ARTS-Laboratory/Sensor-Package-Access-Hub/system_development/V0.3.2/ELCT403/nrf24RX_loraTX_TEENSY/water.h

#define MAX_HEIGHT_VAL 14

const char * height_header[] = {"Date",	"Time", "Dist1",	"Dist2",	"Dist3",	"Dist4",	"Dist5",	"Avg Dist (cm)",
                         "Temp (C)",	"Humidity",	"Pressure",	"Voltage",	"Current (mA)",	"Power (mW)"};
/*
12/1/2025 12:40		-->		1764610800
12/1/2025 12:45		-->		1764611100
12/1/2025 13:00		-->		1764612000
12/1/2025 13:15		-->		1764612900
12/1/2025 13:30		-->		1764613800
*/

double height_data[5][MAX_HEIGHT_VAL] = {
	{{1764610800.0},	{49.03},	{40.90},  {36.14},	{50.11},	{48.21},	{44.88},	{14.63},	{60.11},	{1025.03},	{8.36},	{52.10},	{436.00}, {0}},
	{{1764611100.0},	{16.67},	{15.69},	{16.02},	{16.02},	{16.02},	{16.08},	{15.88},	{58.37},	{1024.99},	{8.37},	{52.50},	{440.00}, {0}},
	{{1764612000.0},	{119.93},	{119.95},	{120.77},	{120.75},	{120.77},	{120.43},	{17.03},	{55.03},	{1025.02},	{8.39},	{28.50},	{240.00}, {0}},
	{{1764612900.0},	{120.77},	{119.48},	{119.47},	{119.96},	{119.14},	{119.77},	{17.07},	{54.79},	{1025.08},	{8.39},	{29.10},	{246.00}, {0}},
	{{1764613800.0},	{119.95},	{119.95},	{119.95},	{119.96},	{120.87},	{120.14},	{16.90},	{55.00},	{1025.01},	{8.39},	{29.00},	{242.00}, {0}}
};
